josh-turnipseed/NIU_Senior_Design_22-23_Group33/Pictures/MIDI_to_CV.jpg

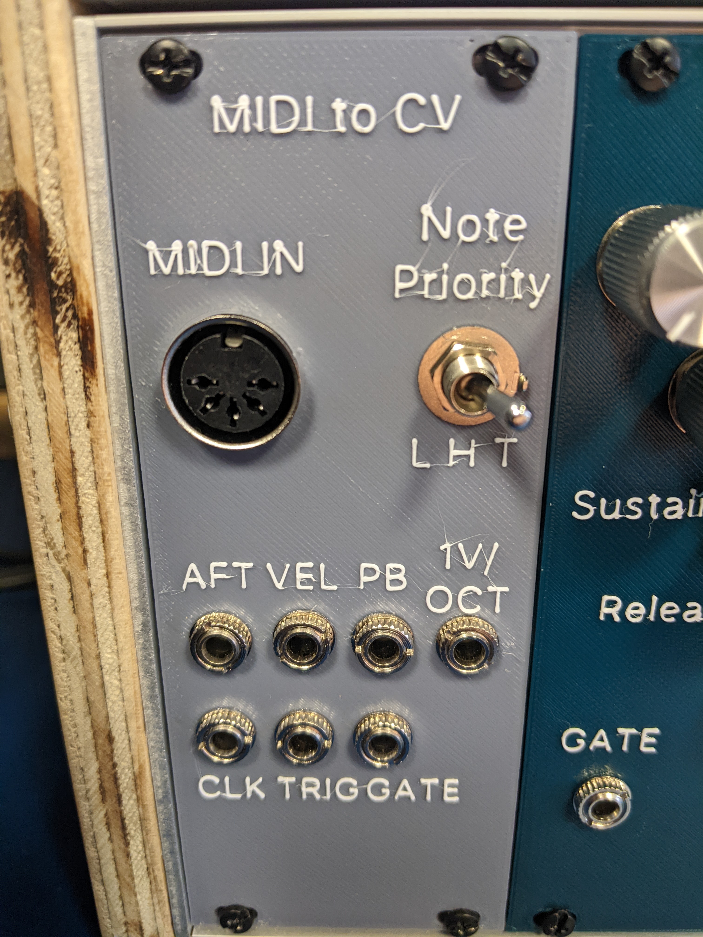
Pictures/MIDI_to_CV.jpg
