josh-turnipseed/NIU_Senior_Design_22-23_Group33/KiCad Schematics/Midi2cv/Midi2cv.kicad_pcb

## KiCad design KiCad Schematics/Midi2cv/Midi2cv.kicad_pcb (2023-05-11)

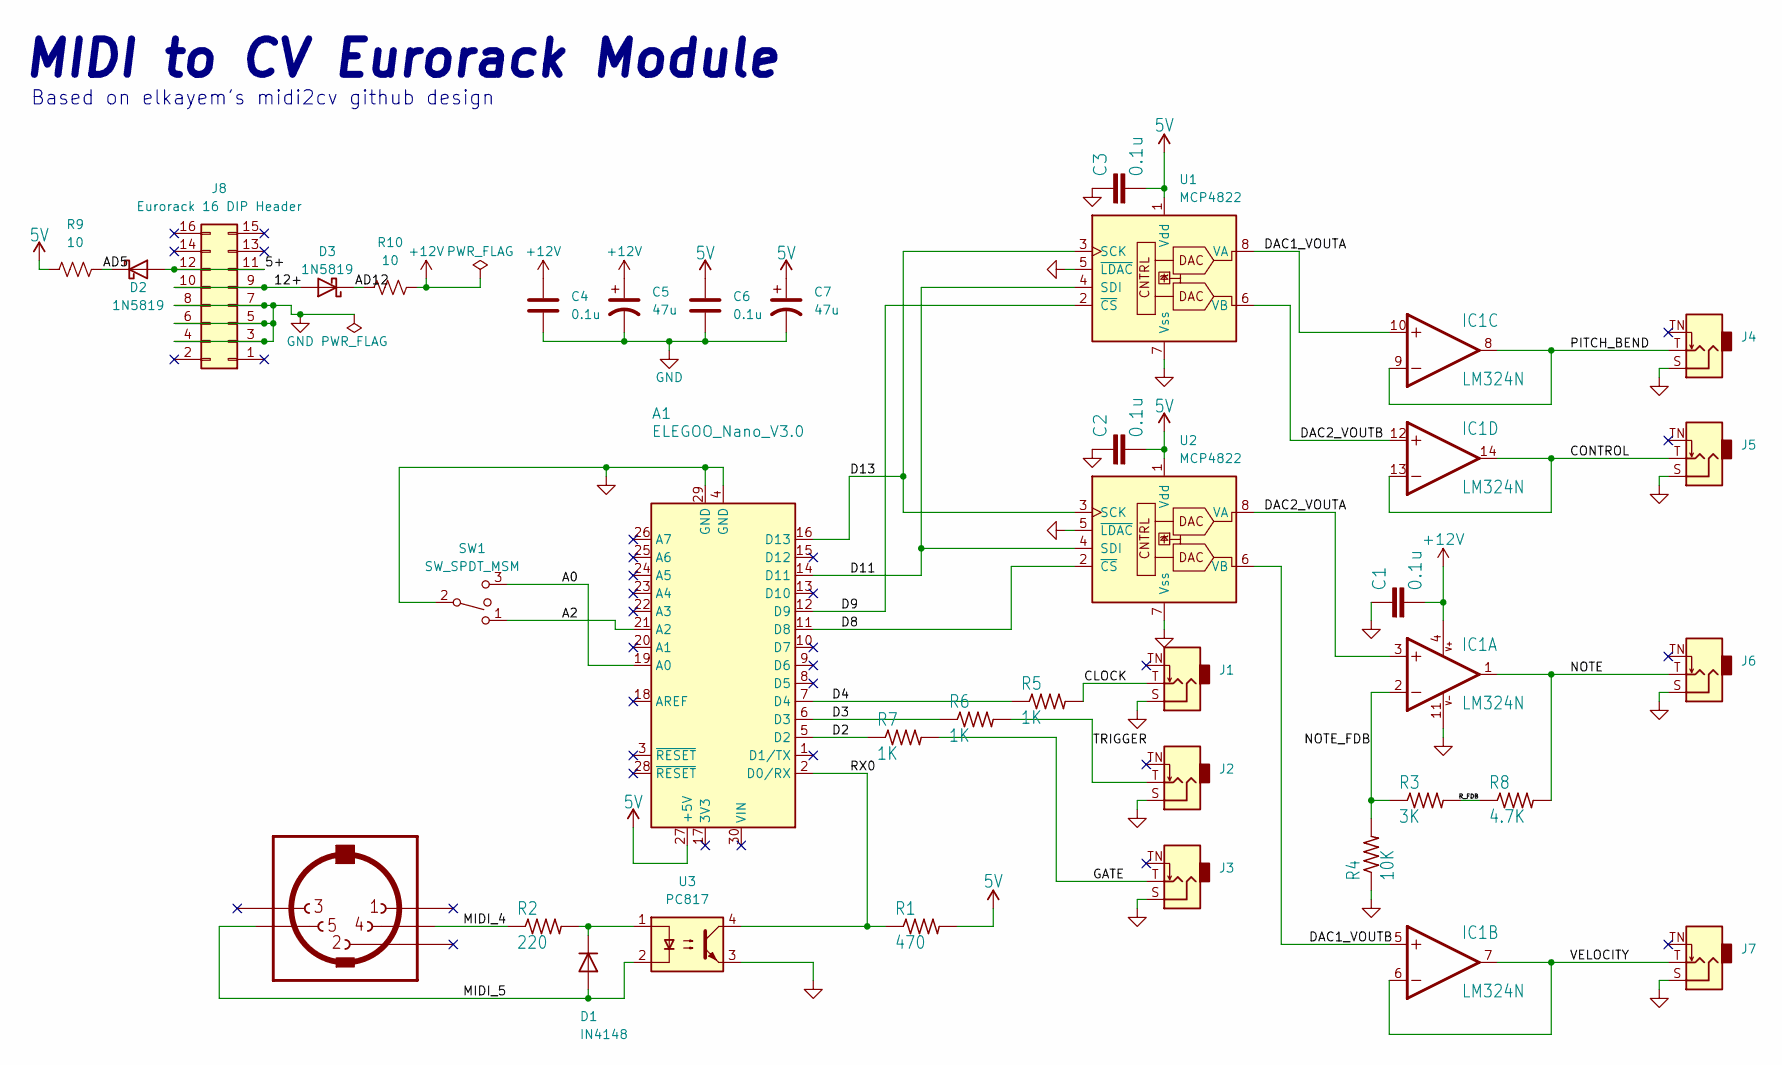
[picture p40: schematic Midi2cv.kicad_sch, MIDI to CV Eurorack Module]

Parts:
A1: ELEGOO_Nano_V3.0; Arduino_Nano
C1, C2, C3, C4, C6: 0.1u; C_Disc_D4.7mm_W2.5mm_P5.00mm
C5, C7: 47u; CP_Radial_D4.0mm_P1.50mm
D1: IN4148; D_DO-35_SOD27_P7.62mm_Horizontal
D2, D3: 1N5819; D_DO-41_SOD81_P10.16mm_Horizontal
IC1: LM324N; DIP-14_W7.62mm
J1: Clock; Jack_3.5mm_QingPu_WQP-PJ398SM_Vertical_CircularHoles
J2: Trigger; Jack_3.5mm_QingPu_WQP-PJ398SM_Vertical_CircularHoles
J3: Gate; Jack_3.5mm_QingPu_WQP-PJ398SM_Vertical_CircularHoles
J4: Pitch Bend; Jack_3.5mm_QingPu_WQP-PJ398SM_Vertical_CircularHoles
J5: Continuous Control; Jack_3.5mm_QingPu_WQP-PJ398SM_Vertical_CircularHoles
J6: Note; Jack_3.5mm_QingPu_WQP-PJ398SM_Vertical_CircularHoles
J7: Velocity; Jack_3.5mm_QingPu_WQP-PJ398SM_Vertical_CircularHoles
J8: Eurorack 16 DIP Header; Eurorack_16_pin_header
R1: 470; R_Axial_DIN0207_L6.3mm_D2.5mm_P7.62mm_Horizontal
R2: 220; R_Axial_DIN0207_L6.3mm_D2.5mm_P7.62mm_Horizontal
R3: 3K; R_Axial_DIN0207_L6.3mm_D2.5mm_P7.62mm_Horizontal
R4: 10K; R_Axial_DIN0207_L6.3mm_D2.5mm_P7.62mm_Horizontal
R5, R6, R7: 1K; R_Axial_DIN0207_L6.3mm_D2.5mm_P7.62mm_Horizontal
R8: 4.7K; R_Axial_DIN0207_L6.3mm_D2.5mm_P7.62mm_Horizontal
R9, R10: 10; R_Axial_DIN0207_L6.3mm_D2.5mm_P7.62mm_Horizontal
SW1: SW_SPDT_MSM; SPDT toggle on-off-on
U1, U2: MCP4822; DIP-8_W7.62mm
U3: PC817; DIP-4_W7.62mm
U$1: MIDIJACK; CUI_SD-50BV

Connections:
5V: A1.27 (+5V), C2.2, C3.2, C6.2, C7.1, R1.2, R9.2, U1.1 (Vdd), U2.1 (Vdd)
+12V: C1.2, C4.2, C5.1, IC1.4 (V+), R10.1
/5+: D2.2 (A), J8.11, J8.12
/12+: D3.2 (A), J8.9, J8.10
/A0: A1.19 (A0), SW1.3
/A2: A1.21 (A2), SW1.1
/AD5: D2.1 (K), R9.1
/AD12: D3.1 (K), R10.2
/CLOCK: J1.T, R5.2
/CONTROL: IC1.13 (-IN), IC1.14 (OUT), J5.T
/D2: A1.5 (D2), R7.1
/D3: A1.6 (D3), R6.1
/D4: A1.7 (D4), R5.1
/D8: A1.11 (D8), U2.2 (~CS)
/D9: A1.12 (D9), U1.2 (~CS)
/D11: A1.14 (D11), U1.4 (SDI), U2.4 (SDI)
/D13: A1.16 (D13), U1.3 (SCK), U2.3 (SCK)
/DAC1_VOUTA: IC1.10 (+IN), U1.8 (VA)
/DAC1_VOUTB: IC1.5 (+IN), U2.6 (VB)
/DAC2_VOUTA: IC1.3 (+IN), U2.8 (VA)
/DAC2_VOUTB: IC1.12 (+IN), U1.6 (VB)
/GATE: J3.T, R7.2
/MIDI_4: R2.1, U$1.4
/MIDI_5: D1.2 (A), U3.2, U$1.5
/NOTE: IC1.1 (OUT), J6.T, R8.2
/NOTE_FDB: IC1.2 (-IN), R3.1, R4.2
/PITCH_BEND: IC1.8 (OUT), IC1.9 (-IN), J4.T
/RX0: A1.2 (D0/RX), R1.1, U3.4
/R_FDB: R3.2, R8.1
/TRIGGER: J2.T, R6.2
/VELOCITY: IC1.6 (-IN), IC1.7 (OUT), J7.T
GND: A1.4 (GND), A1.29 (GND), C1.1, C2.1, C3.1, C4.1, C5.2, C6.1, C7.2, IC1.11 (V-), J1.S, J2.S, J3.S, J4.S, J5.S, J6.S, J7.S, J8.3, J8.4, J8.5, J8.6, J8.7, J8.8, R4.1, SW1.2, U1.5 (~LDAC), U1.7 (Vss), U2.5 (~LDAC), U2.7 (Vss), U3.3
unnamed: D1.1 (K), R2.2, U3.1

Notes on the sheet:
Based on elkayem's midi2cv github design
MIDI to CV Eurorack Module

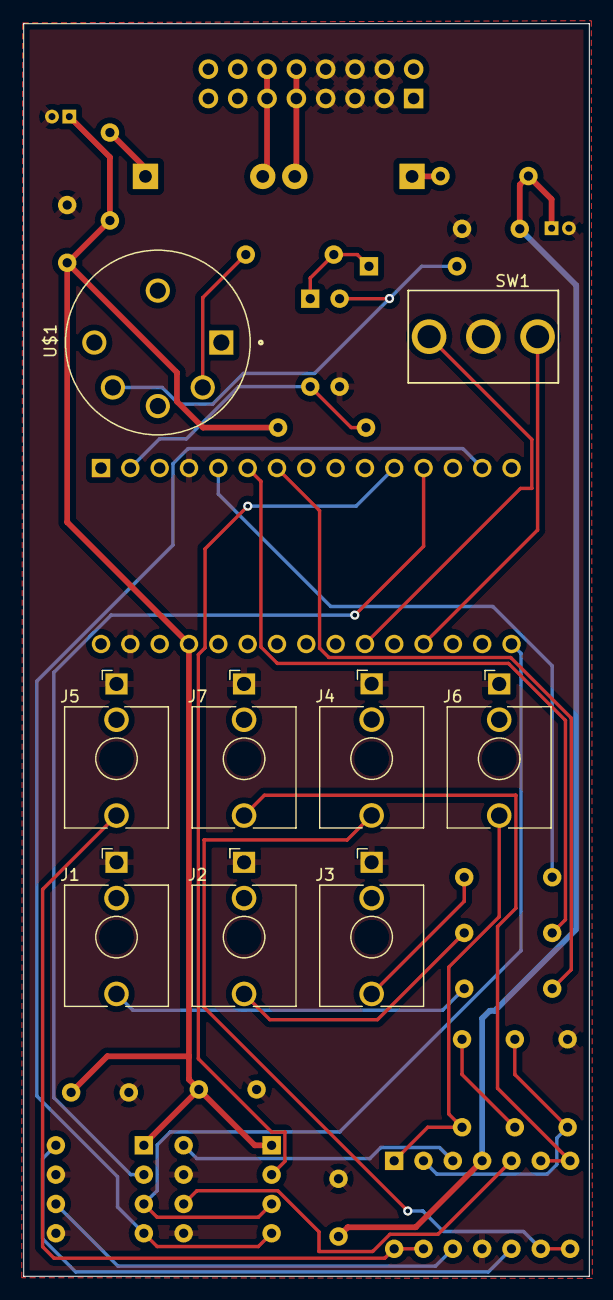
[picture p41: board Midi2cv.kicad_pcb from above]

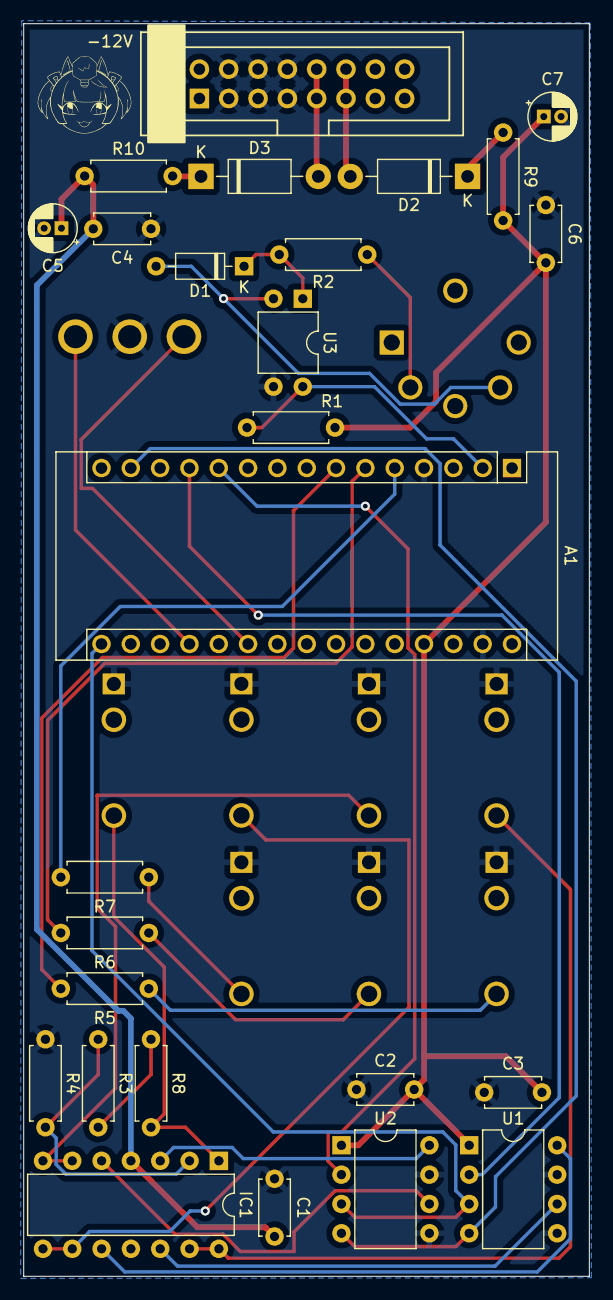
[picture p42: board Midi2cv.kicad_pcb from below]

Board: 2 copper layers, 49.0 x 108.5 mm, 35 parts (26 on the bottom side), 33 nets.
