josh-turnipseed/NIU_Senior_Design_22-23_Group33/KiCad Schematics/ASDR/ASDR_PANEL.kicad_pcb

## KiCad design KiCad Schematics/ASDR/ASDR_PANEL.kicad_pcb (2023-05-11)

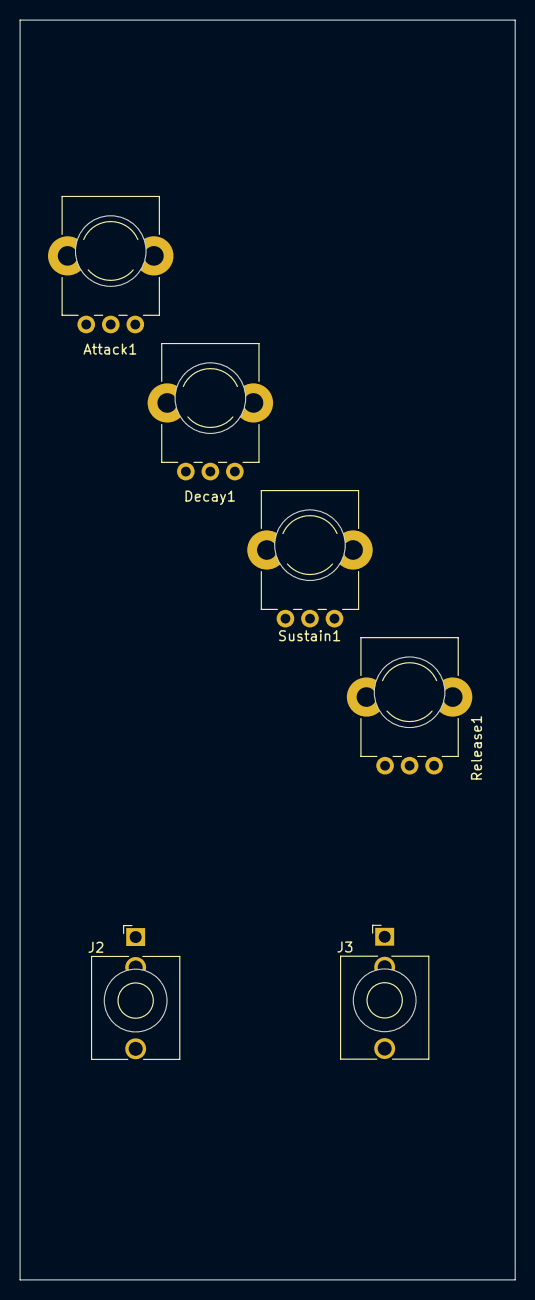
[picture p43: board ASDR_PANEL.kicad_pcb from above]

Board: 2 copper layers, 50.5 x 128.5 mm, 8 parts (0 on the bottom side), 4 nets, no tracks yet.

Parts:
Attack1: 1M; Alpha_9mm_Potentiometer
Decay1: 500k; Alpha_9mm_Potentiometer
J2: GATE; Jack_3.5mm_QingPu_WQP-PJ398SM_Vertical_CircularHoles
J3: OUT; Jack_3.5mm_QingPu_WQP-PJ398SM_Vertical_CircularHoles
Ref**: Subminiature_Switch; Sub_Miniature_Switch_MountingHole_3.5mm
Ref**#2: Subminiature_Switch; Sub_Miniature_Switch_MountingHole_3.5mm
Release1: 500k; Alpha_9mm_Potentiometer
Sustain1: 500k; Alpha_9mm_Potentiometer

Connections:
GND: J2.S, J2.TN, J3.S
unnamed: Attack1.2, Attack1.3
unnamed: Release1.2, Release1.3
unnamed: Decay1.2, Decay1.3
