josh-turnipseed/NIU_Senior_Design_22-23_Group33/KiCad Schematics/Mult/Mult done.kicad_pcb

## KiCad design KiCad Schematics/Mult/Mult done.kicad_pcb (2023-05-11)

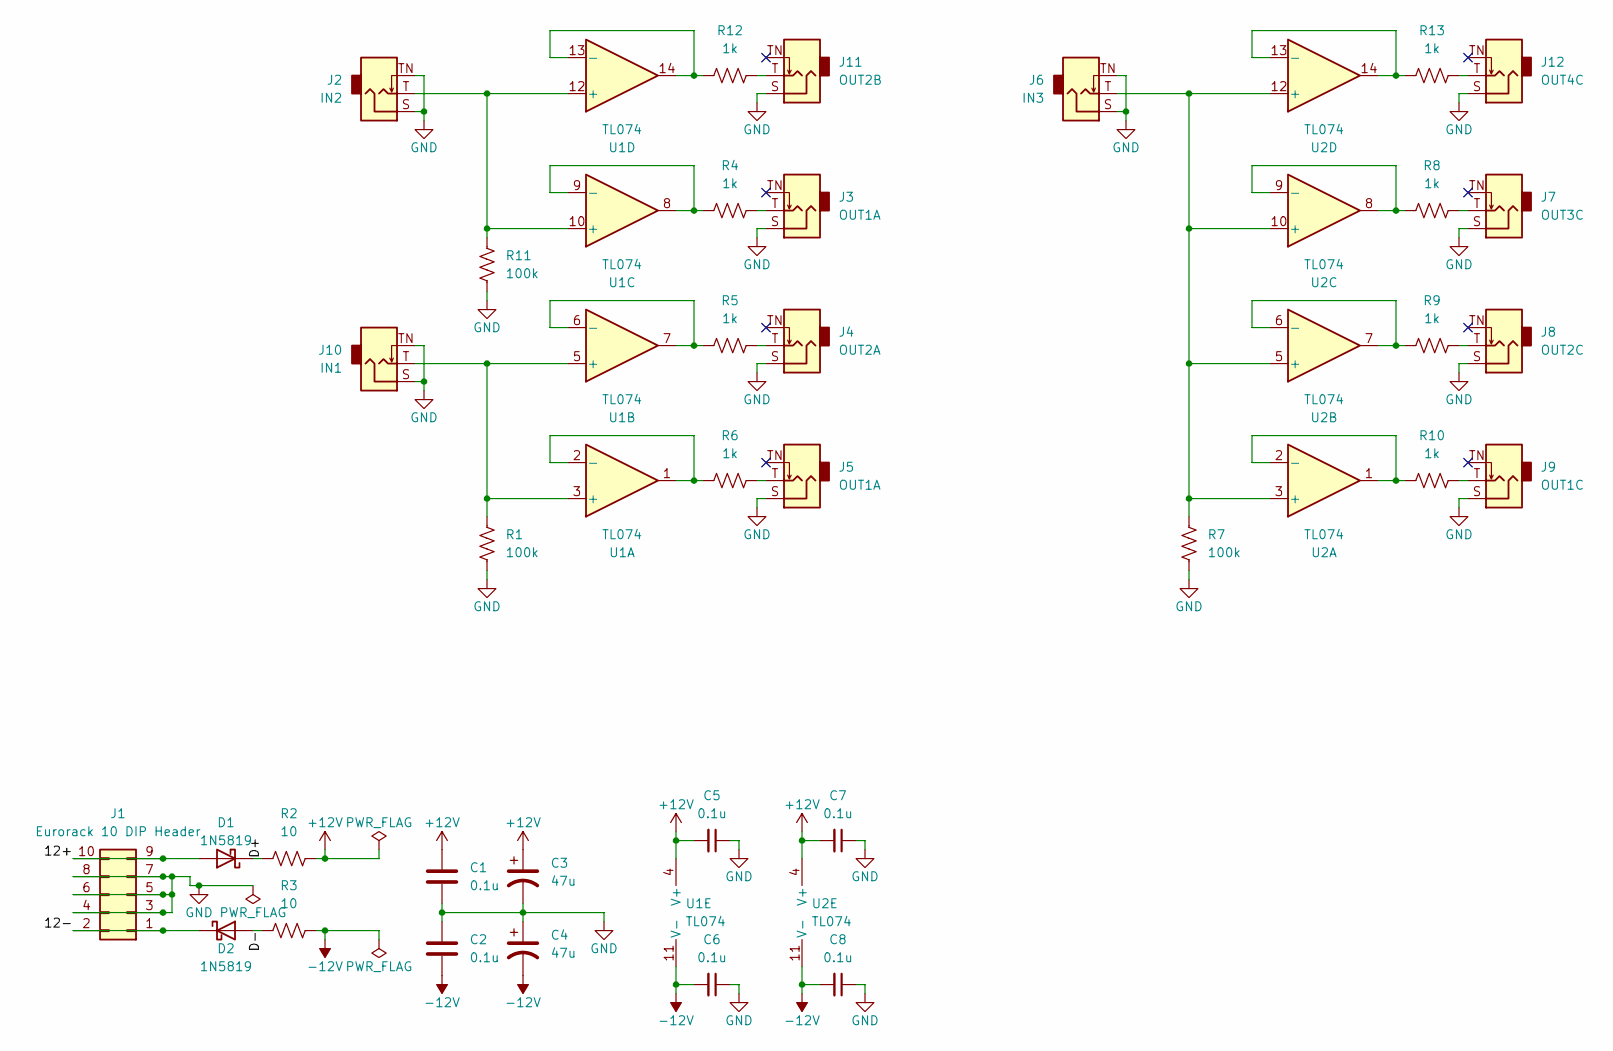
[picture p44: schematic Mult.kicad_sch]

Parts:
C1, C2, C5, C6, C7, C8: 0.1u; C_Disc_D4.7mm_W2.5mm_P5.00mm
C3, C4: 47u; CP_Radial_D4.0mm_P2.00mm
D1, D2: 1N5819; D_DO-41_SOD81_P10.16mm_Horizontal
J1: Eurorack 10 DIP Header; Eurorack_10_pin_header
J2: IN2; Jack_3.5mm_QingPu_WQP-PJ398SM_Vertical_CircularHoles
J3, J5: OUT1A; Jack_3.5mm_QingPu_WQP-PJ398SM_Vertical_CircularHoles
J4: OUT2A; Jack_3.5mm_QingPu_WQP-PJ398SM_Vertical_CircularHoles
J6: IN3; Jack_3.5mm_QingPu_WQP-PJ398SM_Vertical_CircularHoles
J7: OUT3C; Jack_3.5mm_QingPu_WQP-PJ398SM_Vertical_CircularHoles
J8: OUT2C; Jack_3.5mm_QingPu_WQP-PJ398SM_Vertical_CircularHoles
J9: OUT1C; Jack_3.5mm_QingPu_WQP-PJ398SM_Vertical_CircularHoles
J10: IN1; Jack_3.5mm_QingPu_WQP-PJ398SM_Vertical_CircularHoles
J11: OUT2B; Jack_3.5mm_QingPu_WQP-PJ398SM_Vertical_CircularHoles
J12: OUT4C; Jack_3.5mm_QingPu_WQP-PJ398SM_Vertical_CircularHoles
R1, R7, R11: 100k; R_Axial_DIN0207_L6.3mm_D2.5mm_P7.62mm_Horizontal
R2, R3: 10; R_Axial_DIN0207_L6.3mm_D2.5mm_P7.62mm_Horizontal
R4, R5, R6, R8, R9, R10, R12, R13: 1k; R_Axial_DIN0207_L6.3mm_D2.5mm_P7.62mm_Horizontal
U1, U2: TL074; DIP-14_W7.62mm

Connections:
+12V: C1.2, C3.1, C5.2, C7.2, R2.1, U1.4 (V+), U2.4 (V+)
-12V: C2.1, C4.2, C6.2, C8.2, R3.1, U1.11 (V-), U2.11 (V-)
/12+: D1.2 (A), J1.9, J1.10
/12-: D2.1 (K), J1.1, J1.2
/D+: D1.1 (K), R2.2
/D-: D2.2 (A), R3.2
GND: C1.1, C2.2, C3.2, C4.1, C5.1, C6.1, C7.1, C8.1, J1.3, J1.4, J1.5, J1.6, J1.7, J1.8, J2.S, J2.TN, J3.S, J4.S, J5.S, J6.S, J6.TN, J7.S, J8.S, J9.S, J10.S, J10.TN, J11.S, J12.S, R1.2, R7.2, R11.2
unnamed: J2.T, R11.1, U1.10 (+), U1.12 (+)
unnamed: J3.T, R4.2
unnamed: J4.T, R5.2
unnamed: J5.T, R6.2
unnamed: J6.T, R7.1, U2.3 (+), U2.5 (+), U2.10 (+), U2.12 (+)
unnamed: J7.T, R8.2
unnamed: J8.T, R9.2
unnamed: J9.T, R10.2
unnamed: J10.T, R1.1, U1.3 (+), U1.5 (+)
unnamed: J11.T, R12.2
unnamed: J12.T, R13.2
unnamed: R4.1, U1.8, U1.9 (-)
unnamed: R5.1, U1.6 (-), U1.7
unnamed: R6.1, U1.1, U1.2 (-)
unnamed: R8.1, U2.8, U2.9 (-)
unnamed: R9.1, U2.6 (-), U2.7
unnamed: R10.1, U2.1, U2.2 (-)
unnamed: R12.1, U1.13 (-), U1.14
unnamed: R13.1, U2.13 (-), U2.14

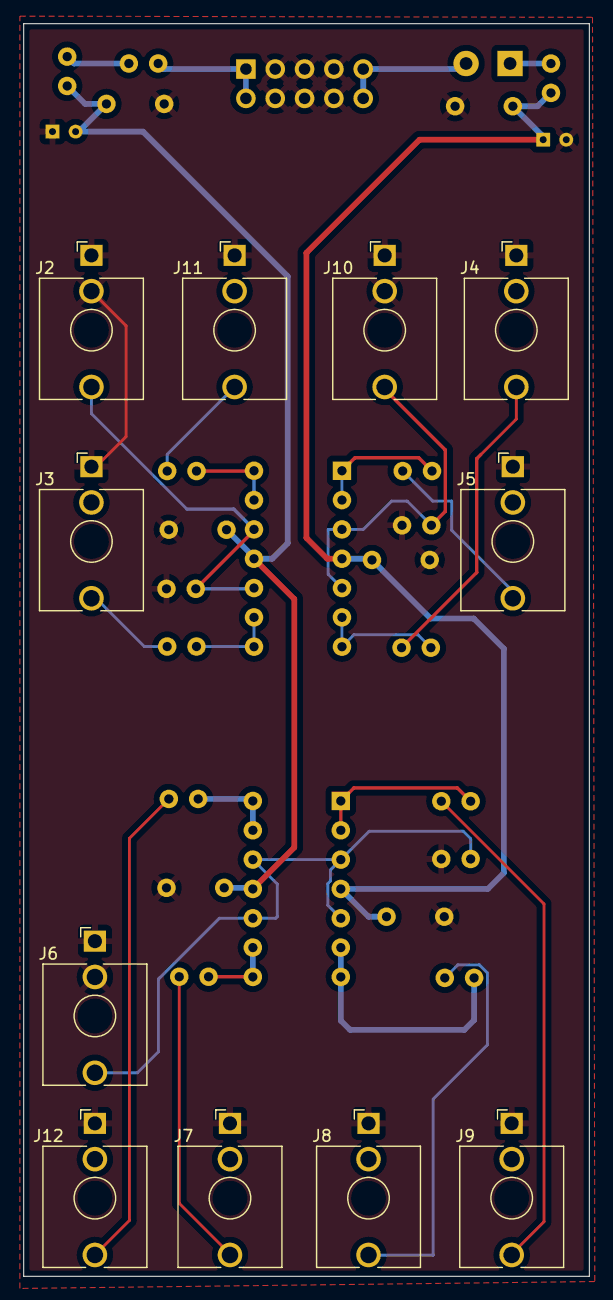
[picture p45: board Mult done.kicad_pcb from above]

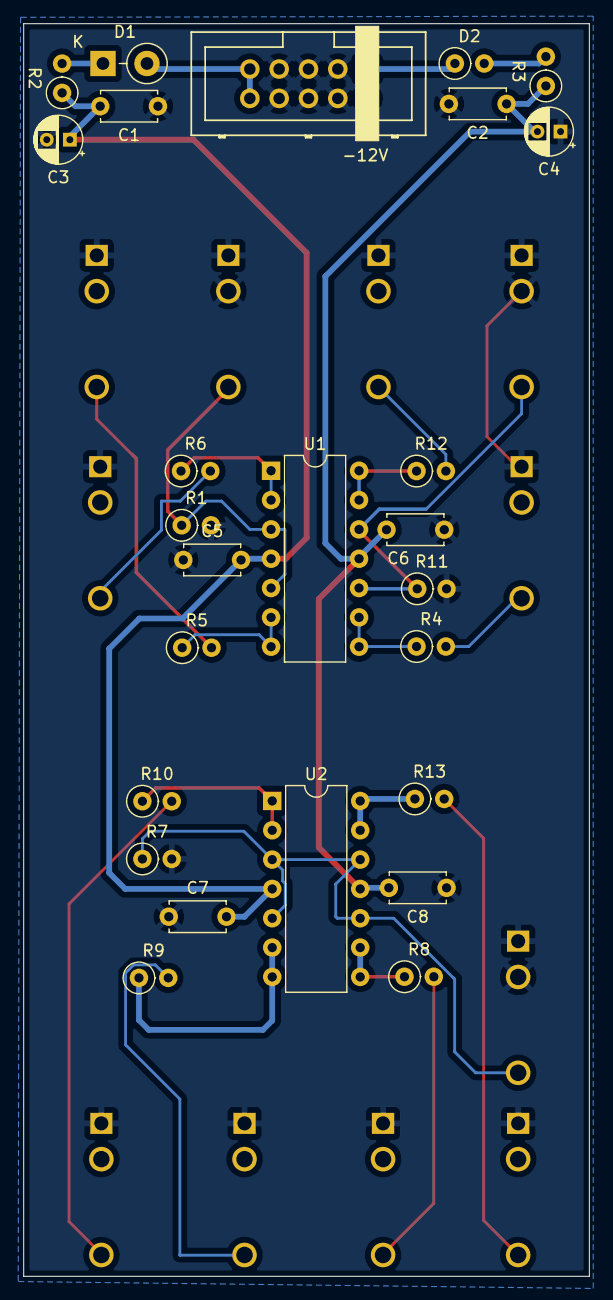
[picture p46: board Mult done.kicad_pcb from below]

Board: 2 copper layers, 49.0 x 108.5 mm, 37 parts (26 on the bottom side), 26 nets.
