josh-turnipseed/NIU_Senior_Design_22-23_Group33/KiCad Schematics/VCO/VCO_INTERFACE_PANEL.kicad_pcb

## KiCad design KiCad Schematics/VCO/VCO_INTERFACE_PANEL.kicad_pcb (2023-05-11)

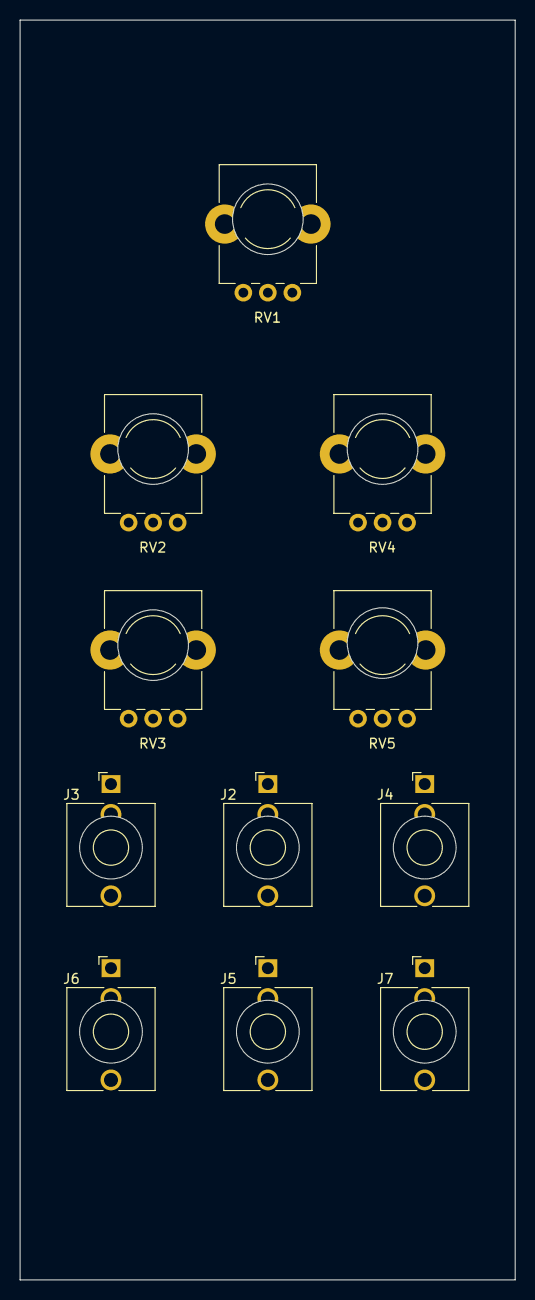
[picture p47: board VCO_INTERFACE_PANEL.kicad_pcb from above]

Board: 2 copper layers, 50.5 x 128.5 mm, 17 parts (0 on the bottom side), 3 nets, no tracks yet.

Parts:
J2: FM; Jack_3.5mm_QingPu_WQP-PJ398SM_Vertical_CircularHoles
J3: CV; Jack_3.5mm_QingPu_WQP-PJ398SM_Vertical_CircularHoles
J4: PWM; Jack_3.5mm_QingPu_WQP-PJ398SM_Vertical_CircularHoles
J5: Triangle; Jack_3.5mm_QingPu_WQP-PJ398SM_Vertical_CircularHoles
J6: Saw; Jack_3.5mm_QingPu_WQP-PJ398SM_Vertical_CircularHoles
J7: Pulse; Jack_3.5mm_QingPu_WQP-PJ398SM_Vertical_CircularHoles
RV1, RV2: 100K; Alpha_9mm_Potentiometer_Aligned
RV3: 1Meg; Alpha_9mm_Potentiometer_Aligned
RV4: 100k; Alpha_9mm_Potentiometer_Aligned
RV5: 250k; Alpha_9mm_Potentiometer_Aligned
Ref**: Subminiature_Switch; Sub_Miniature_Switch_MountingHole_3.5mm
Ref**#2, Ref**#3, Ref**#4, Ref**#5, Ref**#6: Subminiature_Switch; Sub_Miniature_Switch_MountingHole_3.5mm

Connections:
/FM_pot: RV3.1, RV3.2
/PWM_Pot: J4.T, RV5.1, RV5.2
GND1: J2.S, J2.TN, J3.S, J3.TN, J4.S, J4.TN, J5.S, J6.S, J7.S, RV2.3
